dgrubb/Jaguar-USB-tap/preview/Jaguar-USB-tap_render_back.png

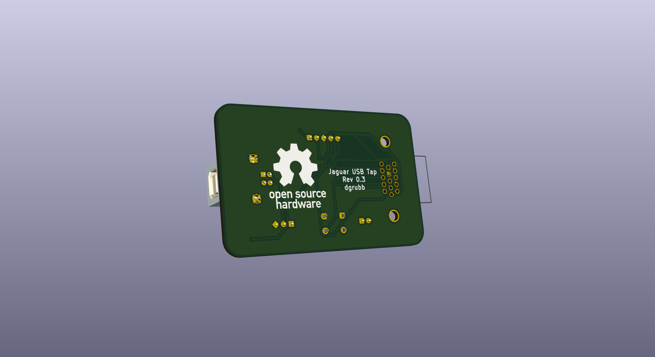
preview/Jaguar-USB-tap_render_back.png
